zezulkaradim/RGB-Display-16-x-16/documentation/ER diagram.jpg

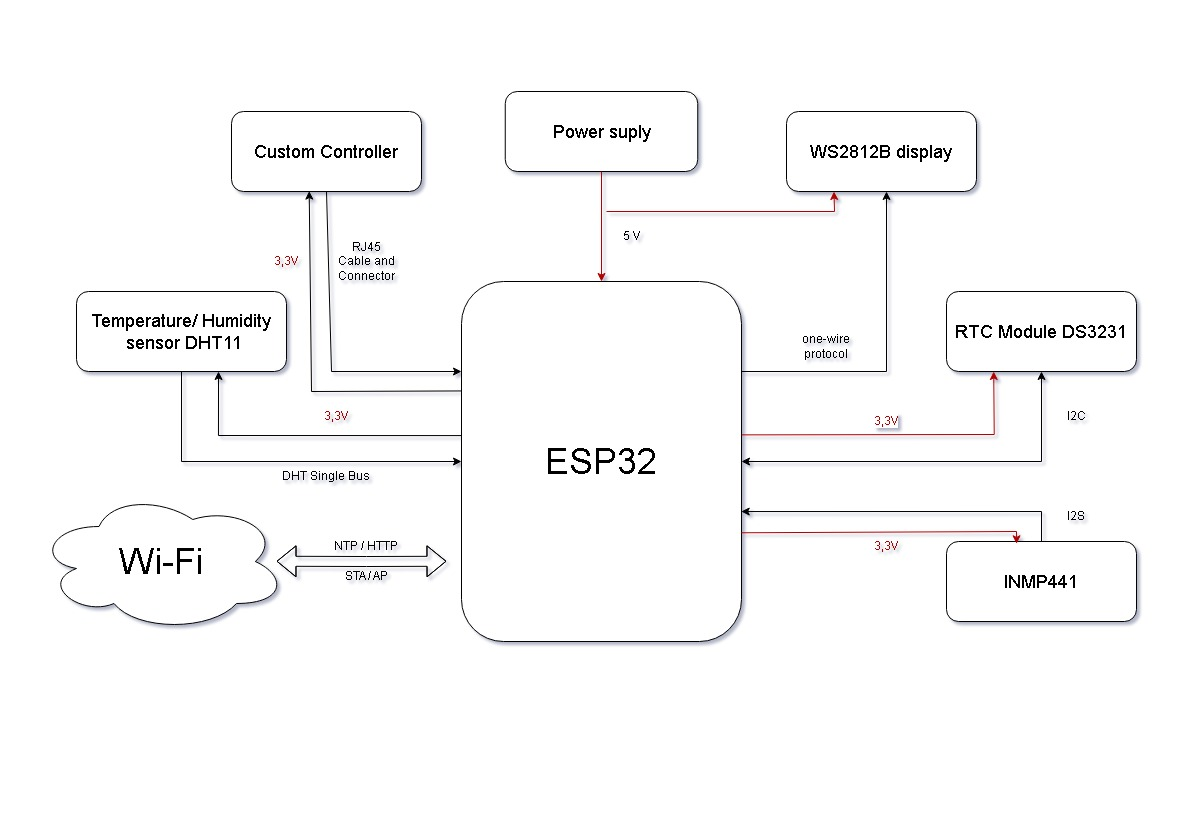
documentation/ER diagram.jpg
