zezulkaradim/RGB-Display-16-x-16/documentation/led strip scheme.png

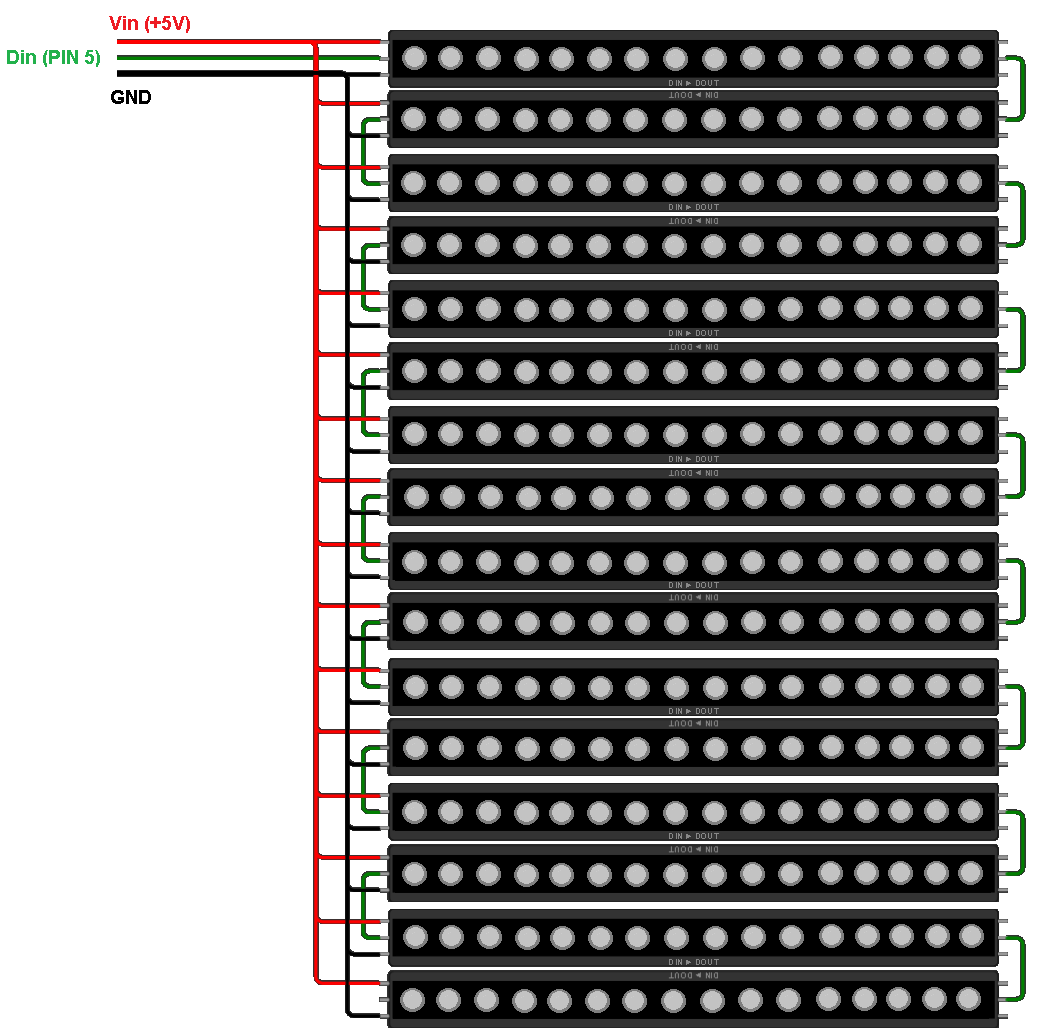
documentation/led strip scheme.png
