zezulkaradim/RGB-Display-16-x-16/Images/20260319_201855.jpg

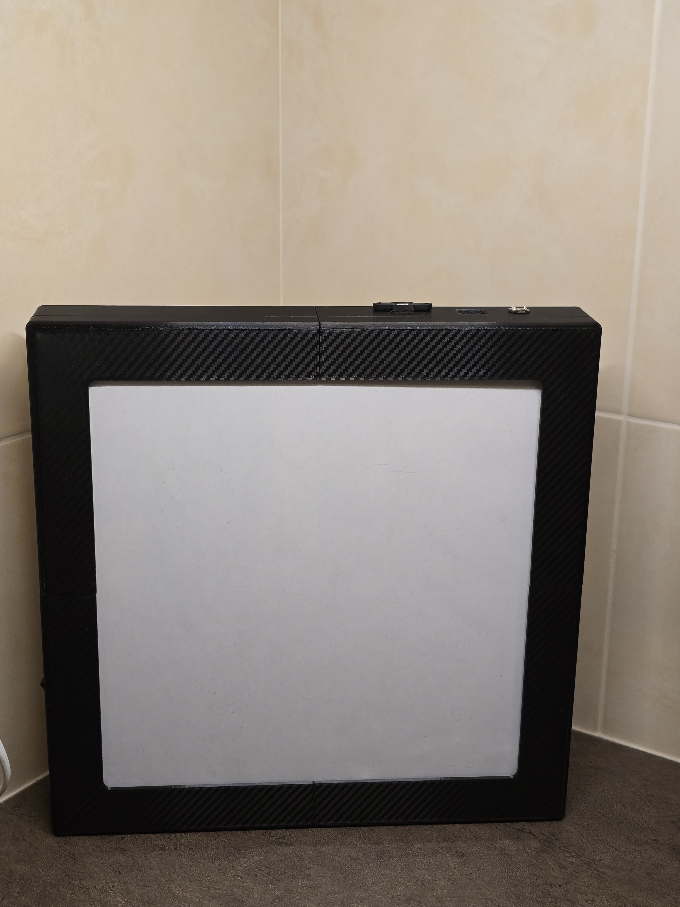
Images/20260319_201855.jpg
