zezulkaradim/RGB-Display-16-x-16/Images/20260319_204947.jpg

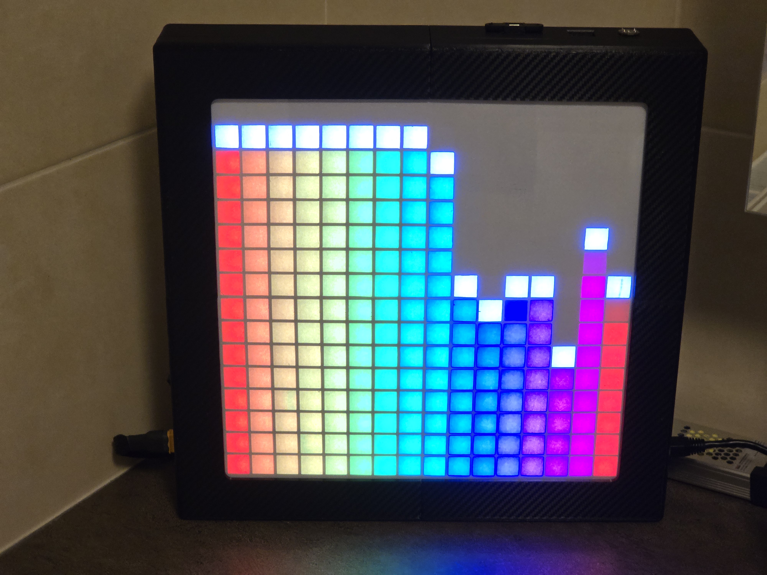
Images/20260319_204947.jpg
